zhu-ziyu/TDJ-Speaker/other/盖子v2.step

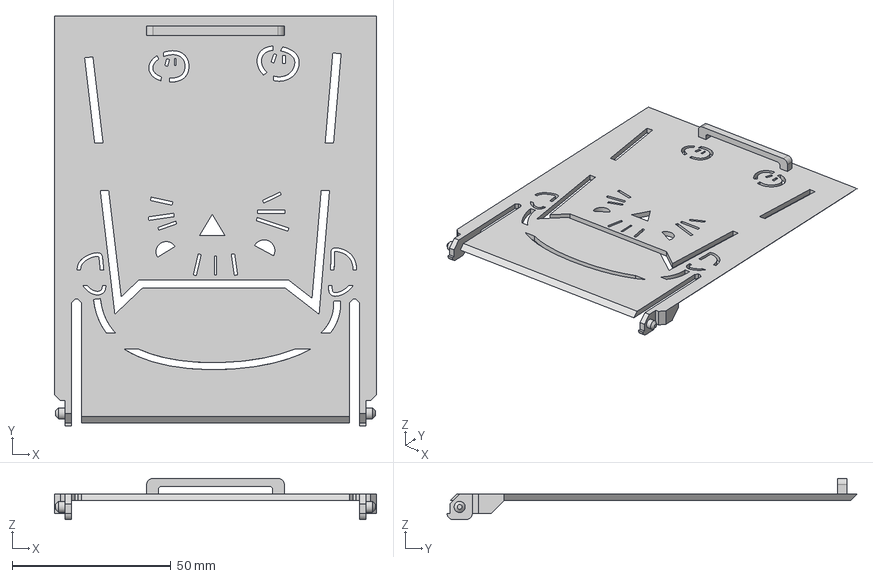
[picture p17: CAD file, 2025-11-04]
other/盖子v2.step
101.7 x 129.2 x 13.0 mm
