zhu-ziyu/TDJ-Speaker/杂/自锁开关16mm.STEP

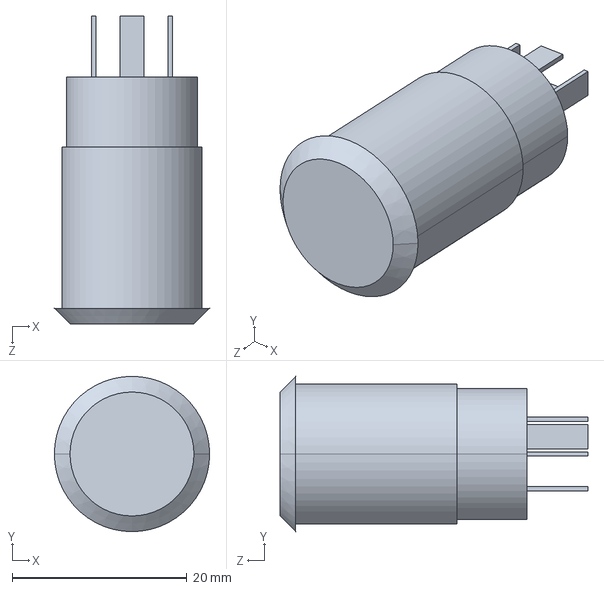
[picture p18: CAD file, 2025-11-04]
杂/自锁开关16mm.STEP
17.8 x 17.8 x 35.3 mm
