zhu-ziyu/TDJ-Speaker/other/diancitiev3.step

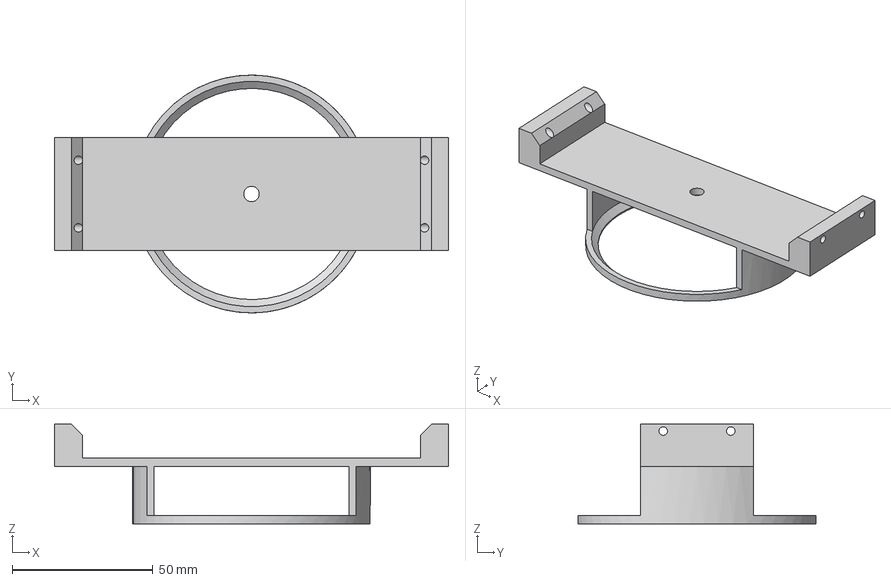
[picture p19: CAD file, 2025-11-04]
other/diancitiev3.step
140.0 x 84.5 x 35.5 mm
