zhu-ziyu/TDJ-Speaker/杂/喇叭.STEP

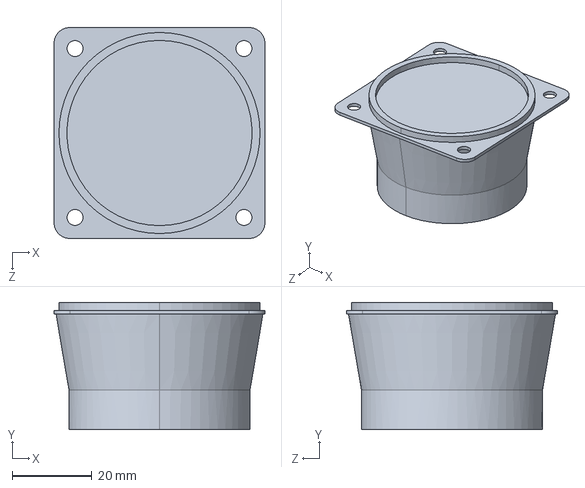
[picture p20: CAD file, 2025-11-04]
杂/喇叭.STEP
53.0 x 32.0 x 53.0 mm
