zhu-ziyu/TDJ-Speaker/waike/按钮头.step

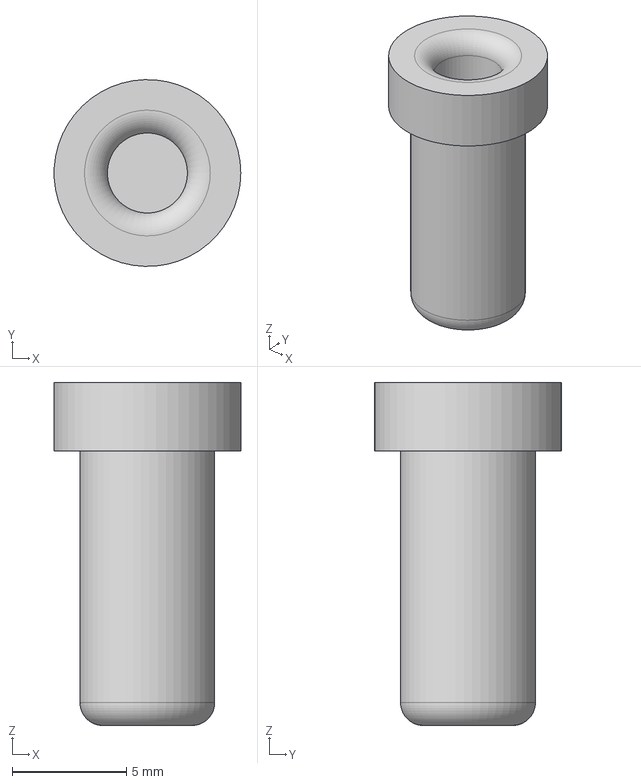
[picture p21: CAD file, 2025-11-04]
waike/按钮头.step
8.16 x 8.16 x 15.0 mm
