zhu-ziyu/TDJ-Speaker/参考文献/磁流体音响/瓶子.SLDPRT

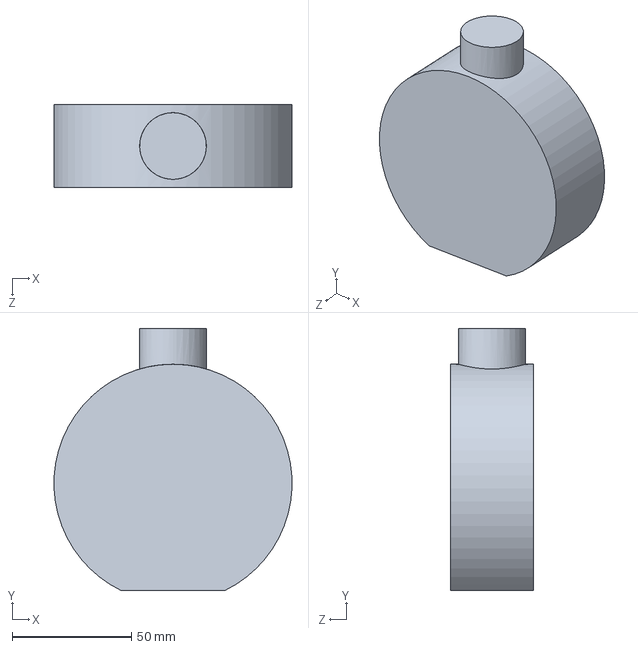
[picture p22: CAD file, 2025-10-06]
参考文献/磁流体音响/瓶子.SLDPRT
99.9 x 110.0 x 35.0 mm
