zhu-ziyu/TDJ-Speaker/waike/盖子.step

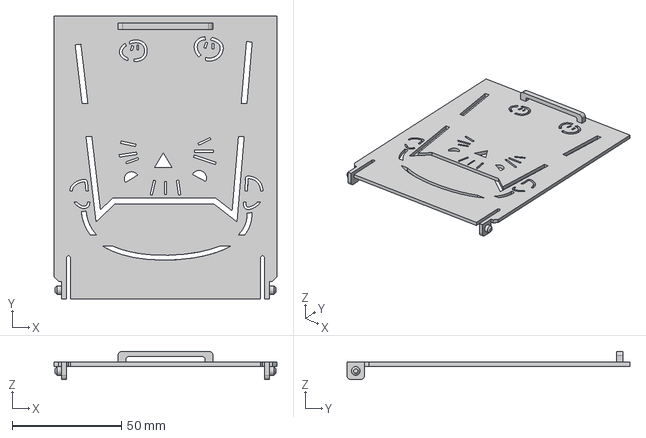
[picture p23: CAD file, 2025-11-04]
waike/盖子.step
101.7 x 129.2 x 13.0 mm
