zhu-ziyu/TDJ-Speaker/other/老师给的音响.step

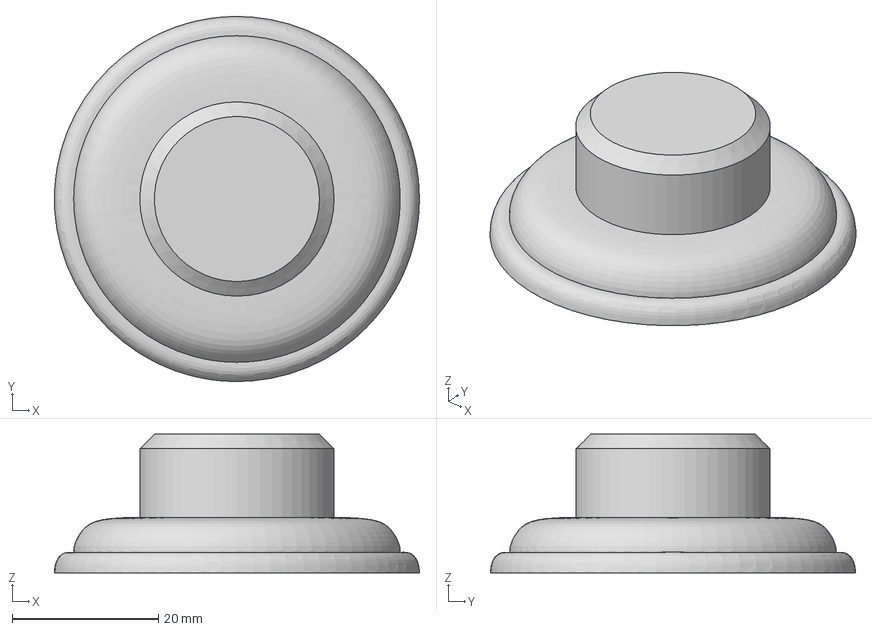
[picture p24: CAD file, 2025-10-27]
other/老师给的音响.step
50.0 x 50.0 x 19.0 mm
