zhu-ziyu/TDJ-Speaker/参考文献/磁流体音响/音响led.SLDPRT

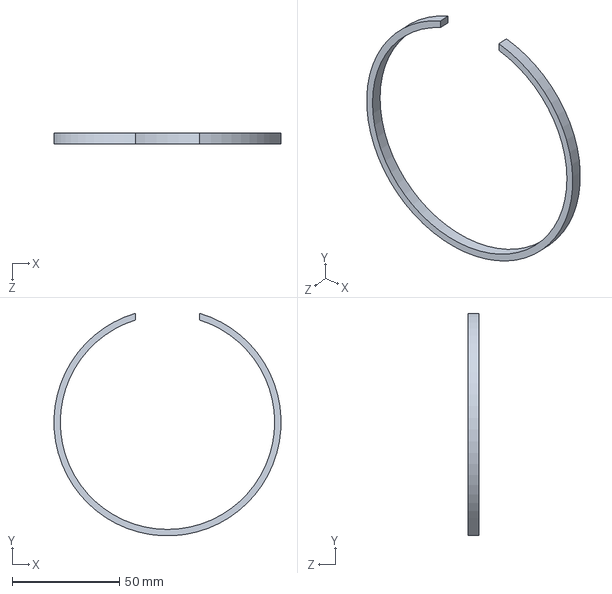
[picture p25: CAD file, 2025-10-06]
参考文献/磁流体音响/音响led.SLDPRT
105.9 x 103.8 x 5.00 mm
