zhu-ziyu/TDJ-Speaker/other/diancitiev1.step

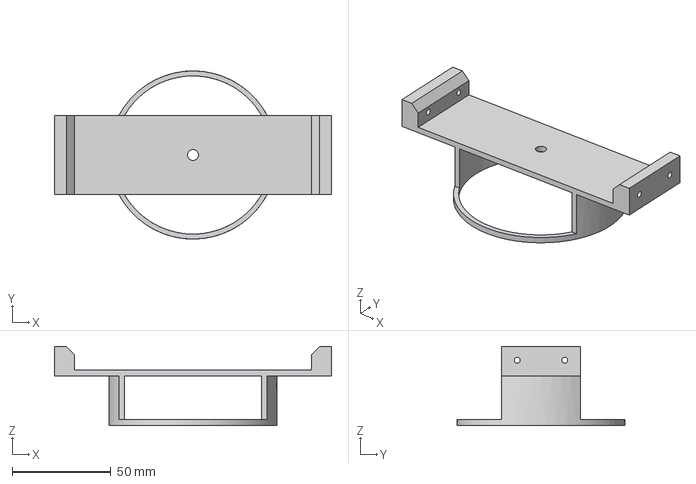
[picture p26: CAD file, 2025-10-21]
other/diancitiev1.step
140.0 x 85.0 x 40.0 mm
