zhu-ziyu/TDJ-Speaker/other/diancitie.step

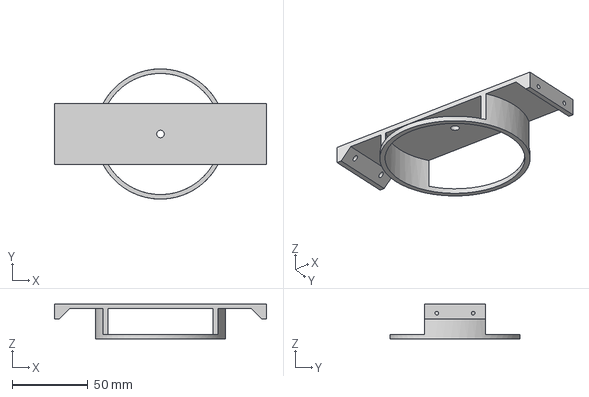
[picture p27: CAD file, 2025-10-21]
other/diancitie.step
140.0 x 86.0 x 23.0 mm
