zhu-ziyu/TDJ-Speaker/waike/backv1.step

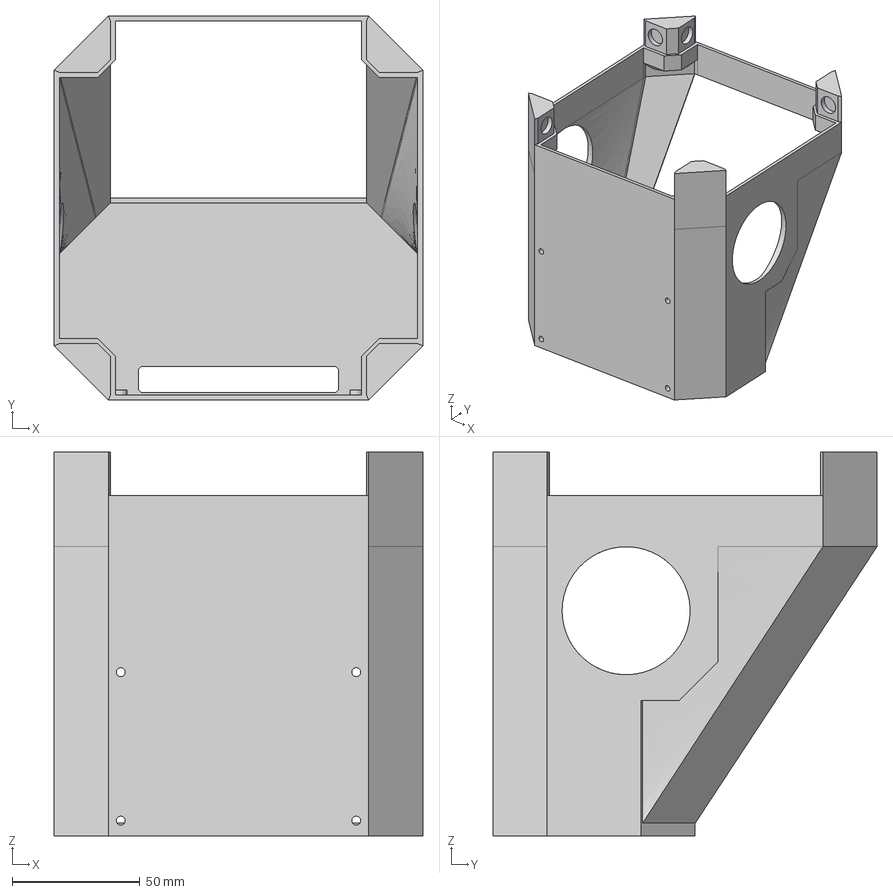
[picture p28: CAD file, 2025-10-21]
waike/backv1.step
144.0 x 150.0 x 150.0 mm
