zhu-ziyu/TDJ-Speaker/other/diancitiev2.step

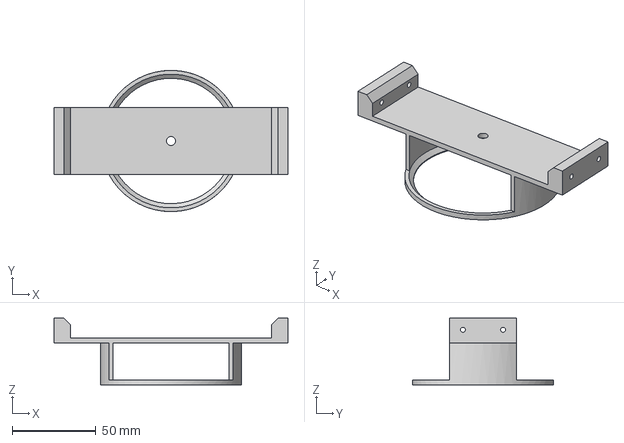
[picture p29: CAD file, 2025-10-21]
other/diancitiev2.step
140.0 x 84.5 x 40.0 mm
