zhu-ziyu/TDJ-Speaker/waike/外壳v1.3mf

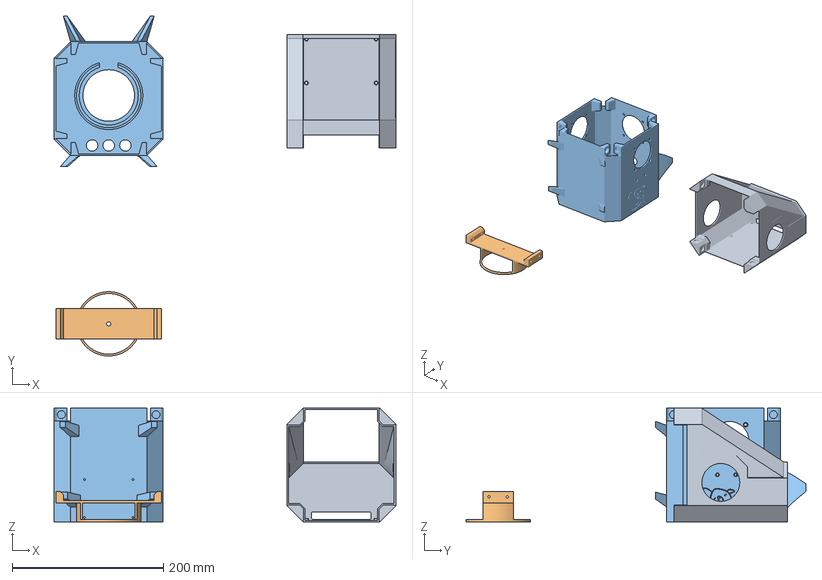
[picture p30: CAD file, 2025-10-21]
waike/外壳v1.3mf
451.2 x 449.2 x 150.0 mm
backv1.step
diancitiev1.step
Techdesign Speaker 3d designv5.step
