zhu-ziyu/TDJ-Speaker/waike/脸上的花纹.stl

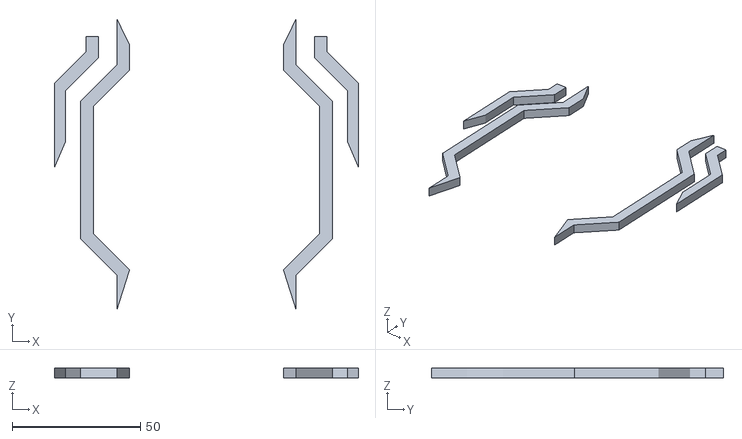
[picture p31: CAD file, 2025-10-20]
waike/脸上的花纹.stl
118.6 x 113.8 x 4.00
