zhu-ziyu/TDJ-Speaker/参考文献/磁流体音响/船开.SLDPRT

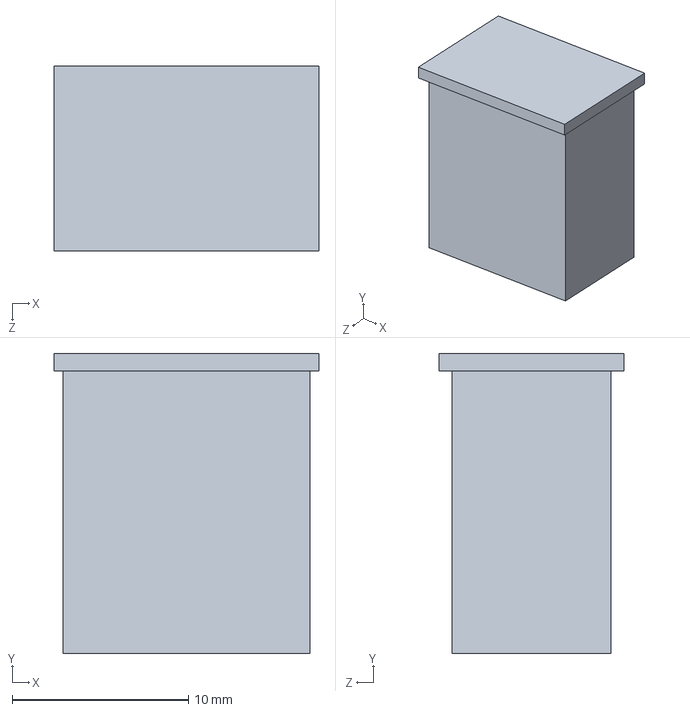
[picture p32: CAD file, 2025-10-06]
参考文献/磁流体音响/船开.SLDPRT
15.0 x 17.0 x 10.5 mm
