zhu-ziyu/TDJ-Speaker/waike/v2.step

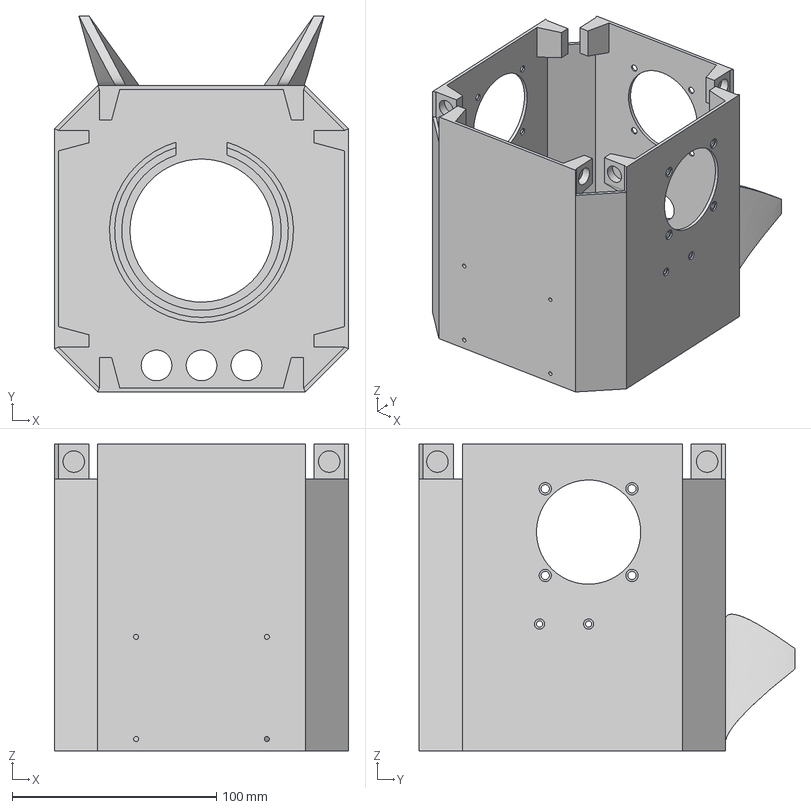
[picture p33: CAD file, 2025-10-19]
waike/v2.step
144.0 x 184.0 x 150.0 mm
